esantanche/wandbox/ToolsCutter.odt

Tools: Cutter

I used a cutter to cut plastic profiles for the box.

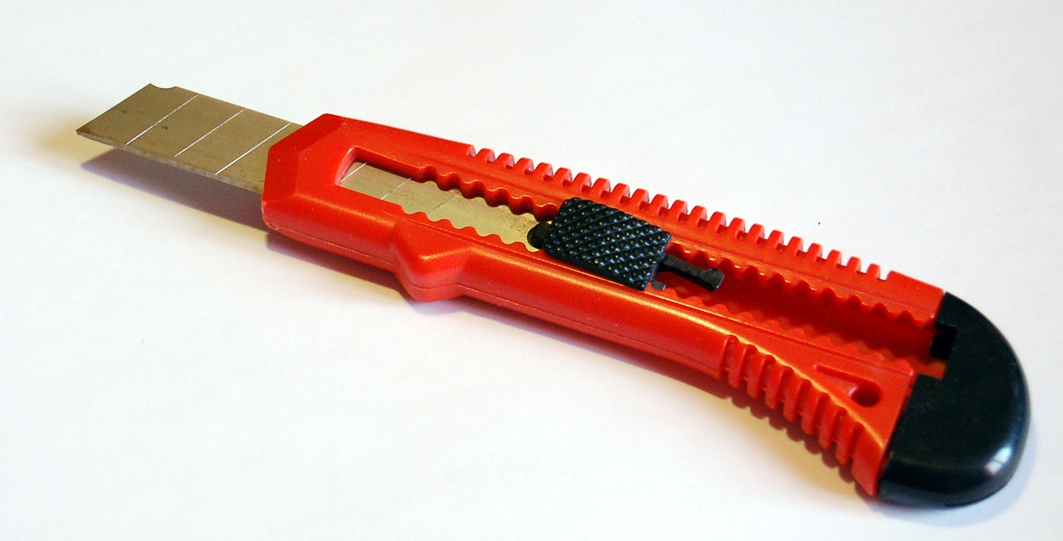
[picture p1: figure]
