esantanche/wandbox/PhotoGallery/011_4mm_box.odt

I changed the drawings to use for the box because I need to use 4mm plywood.

This because I have to use plywood that can be laser cut.

The 6.4mm and 3.2mm plywood I was using in the previous drawings can't be laser cut.

The 3D drawing is basically the same, but now every part is 4mm thick.

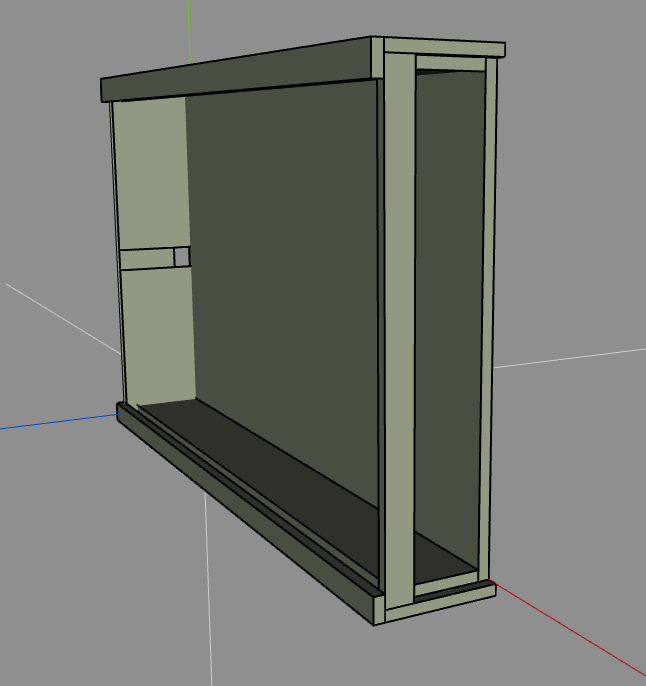
[picture p4: figure]
