esantanche/wandbox/PhotoGallery/010_what_the_box_will_be_like.odt

I started to design the plywood box that will contain Raspberry Pi, monitor and everything.

The 3D design of the box is in the file wandbox-wings3d.wings.

You need the program Wings 3D (http://www.wings3d.com/) to open the file.

I chose Wings 3D because it's simpler to use than other programs.

These are some screen-shots of the box.

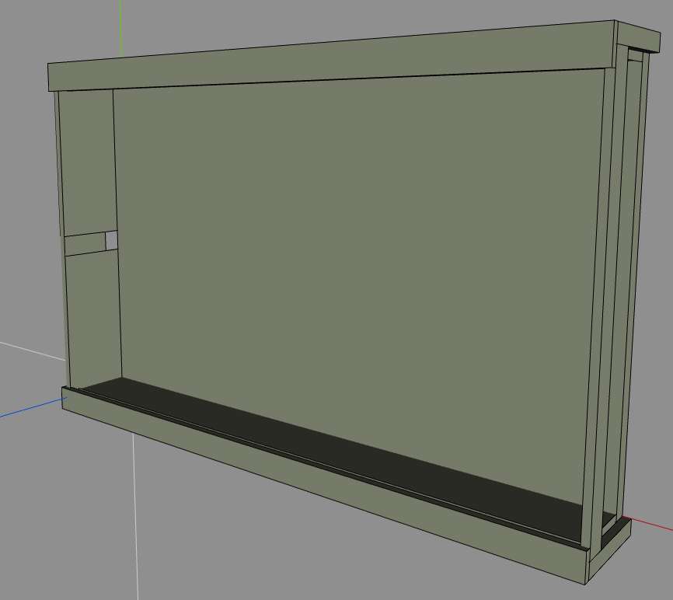
[picture p5: figure]
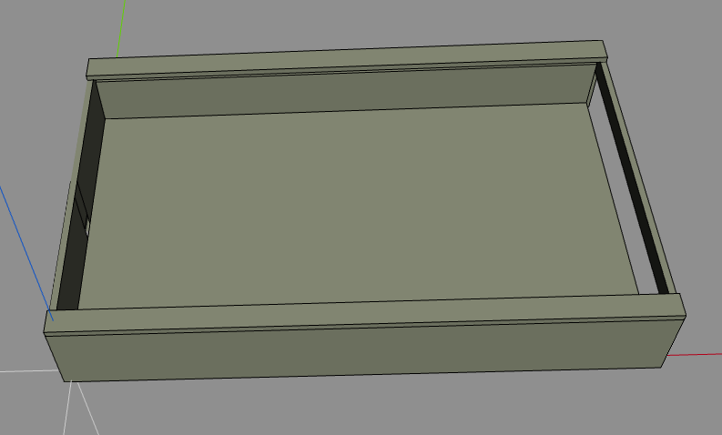
[picture p6: figure]
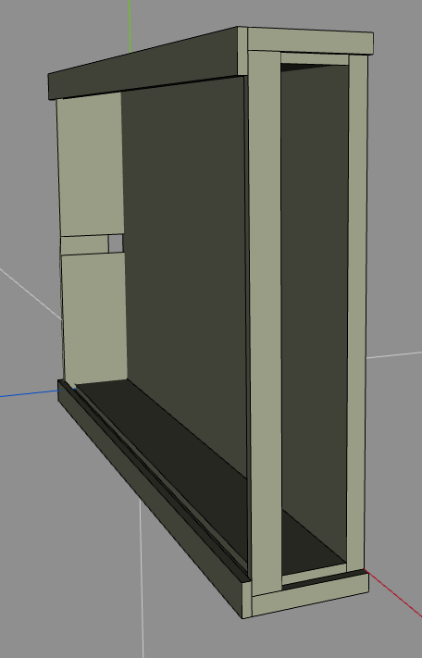
[picture p7: figure]
