esantanche/wandbox/ComponentsFunkyFoamForBatteries.odt

Components:

Funky foam for batteries

Paddybinns (https://www.raspberrypi.org/forums/memberlist.php?mode=viewprofile&u=187239) from https://www.raspberrypi.org/forums recommended I use funky foam to fasten the batteries to the box.

I got this foam from Ryman:

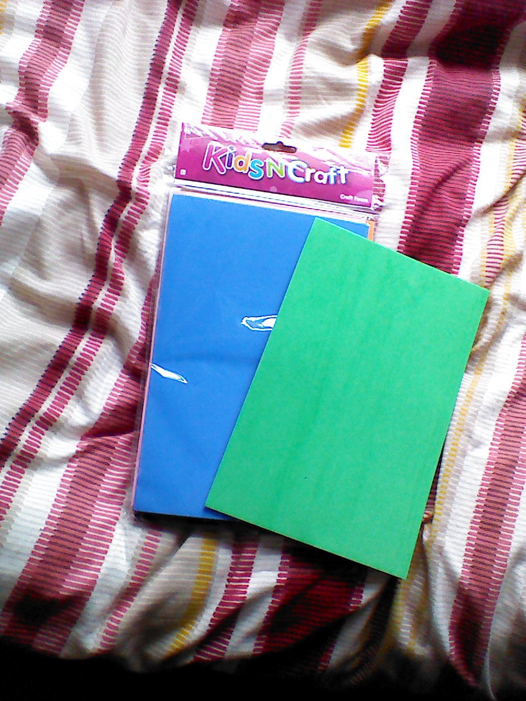
[picture p29: figure]

It's called “Craft Foam”.

It keep the batteries in place very well. I used glue to attach the foam to the wood and to itself.

Other ideas

These are self adhesive: http://www.hobbycraft.co.uk/red-self_adhesive-a4-foam-sheet/571989-1002
