esantanche/wandbox/ComponentsHDMIcable.odt

Components:

HDMI cable

Eventually I got this one:

http://www.cablematic.co.uk/product/HDMI-Cable-HDMI-Type_hyphen_A-Male-to-HDMI_hyphen_A-male-25-cm/

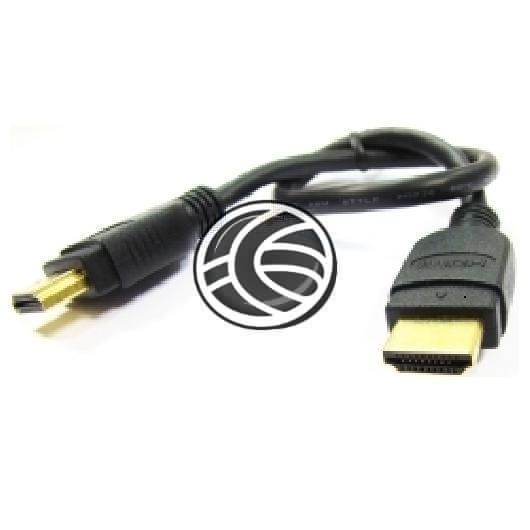
[picture p30: figure]

It's perfect. I had just to move Raspberry Pi and monitor a bit for the cable to fit in.

Before getting this cable I had found a couple of them on Ebay, but they didn't work because the suppliers were sending to me the wrong cable.

They didn't have the 25 cm long one I ordered and sent to me a longer one. But a longer cable was of no use to me because there is little space in the box.
