esantanche/wandbox/ComponentsPowerOnSwitch.odt

Components:

Power on switch

I'm going to use this electronic switch.

You push the micro-button you see on the board and it open or break the circuit.

You apply your power at VIN and you get the output power at VOUT.

From VOUT power goes to Raspberry Pi and monitor. Of course it passes through the voltage regulators first.

You can connect the negative pole to GND on the VIN side and get it on the other side.

The board breaks the GND pole as well, this is better.

This is where the board is from:

http://www.hobbytronics.co.uk/mosfet-power-switch-lv-rev?keyword=switch

I got this board and it came with the pins to be soldered to the board. I'll use connectors to plug into the pins.

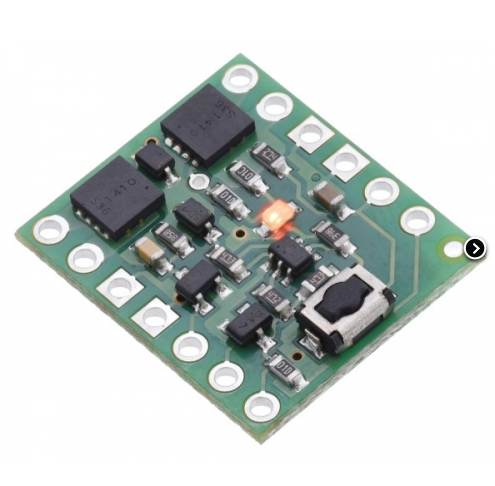
[picture p32: figure]

Connectors

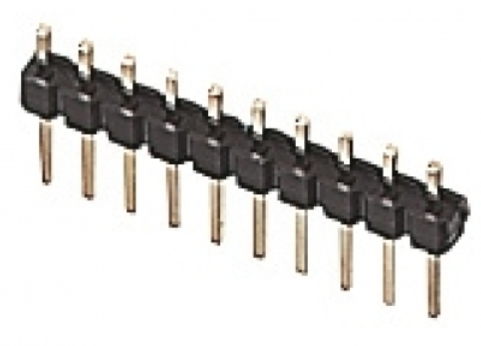
[picture p33: figure]

Pins

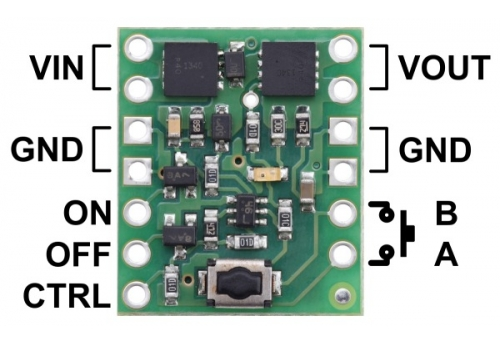
[picture p34: figure]
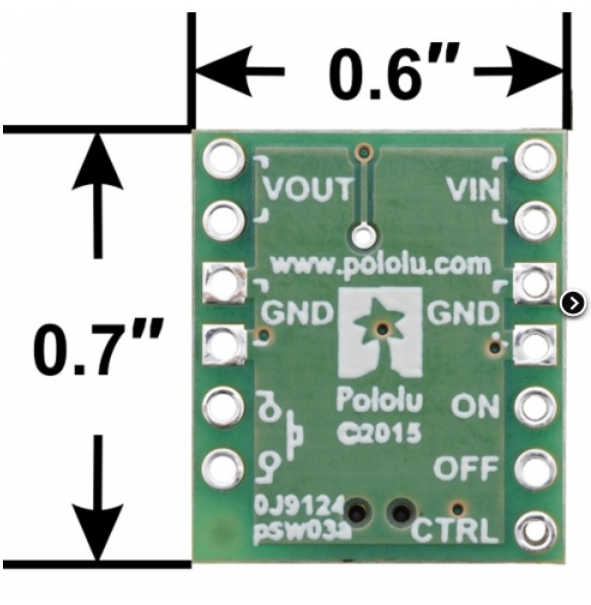
[picture p35: figure]

PIN | Description
A | Connect through momentary switch to pin “B” for standard push-on/push-off operation. Connect through momentary switch to ground for on-only operation.
B | Connect through momentary switch to pin “A” for standard push-on/push-off operation.
ON | A high pulse (> 1 V) on this pin turns on the switch.
OFF | A high pulse (> 1 V) on this pin turns off the switch (e.g. allowing the target device to shut off its own power).
CTRL | This pin directly determines the state of the switch. A high pulse (> 1 V) on this pin turns on the switch; a low pulse (e.g. driving the pin low with a microcontroller output line or pushing a button connected from this pin to ground) turns the switch off. Leave this pin disconnected or floating when not trying to set the switch state. Note that this pin should not be driven high at the same time the “OFF” pin is driven high.
