esantanche/wandbox/ComponentsMonitorAndControlBoard.odt

Components:

Monitor and control board

This is the kit monitor and monitor control board that I bought:

http://www.njytouch.com/products/433-en.html

Some details:

Model: N116B6

This is the control board: http://www.njytouch.com/products/2-en.html.

It has Asian language text for the monitor menu, but I don't care because I'm not going to use the monitor menu.

# Chronology

On 2016-04-02 I got the parcel! I was expecting them not before June!

On 2016-03-19 I asked them if the product is suitable for the UK because I read this on their website:

M.NT68676.2A controller is suitable for Asia-Pacific market. It can support LED/LCD panels which resolution is up to 2048x1152.

On 2016-03-21 they reply saying that the kit is suitable for the UK as well and costs $127 shipping included.

# Information

The monitor should need not more than 20W of power (http://blog.codinghorror.com/how-much-power-does-my-laptop-really-use/). A 2A power supply should be enough. But the maker recommends 4A power supply.

# Package content

1 × HDMI (http://en.wikipedia.org/wiki/HDMI)+DVI (http://en.wikipedia.org/wiki/Digi)+VGA (http://en.wikipedia.org/wiki/Video_Graphics_Array) Controller Board M.NT68676.2A (http://www.njytouch.com/products/2-en.html)

1× 11.6inch 1366* 768 LCD Panel (One of N116B6 (http://www.njytouch.com/products/541-en.html) LP116WH1 B116XW02 LTN116AT01 LTN116AT03 CALL116WA01)

1× LVDS Cable

1× Keyboard with Wire

# Images

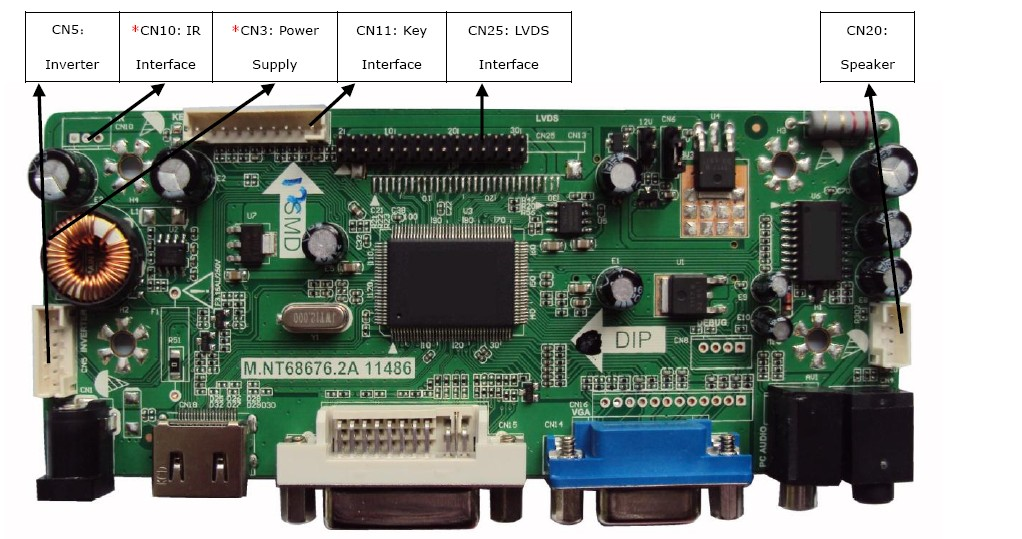
[picture p38: figure]
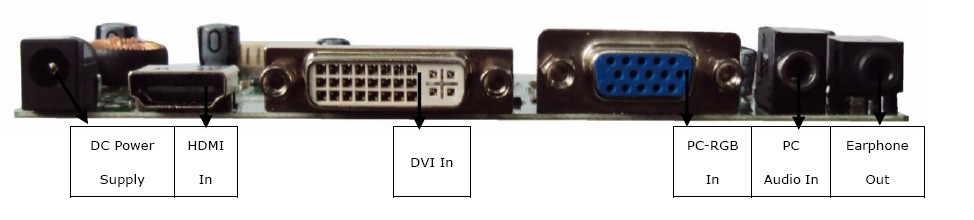
[picture p39: figure]
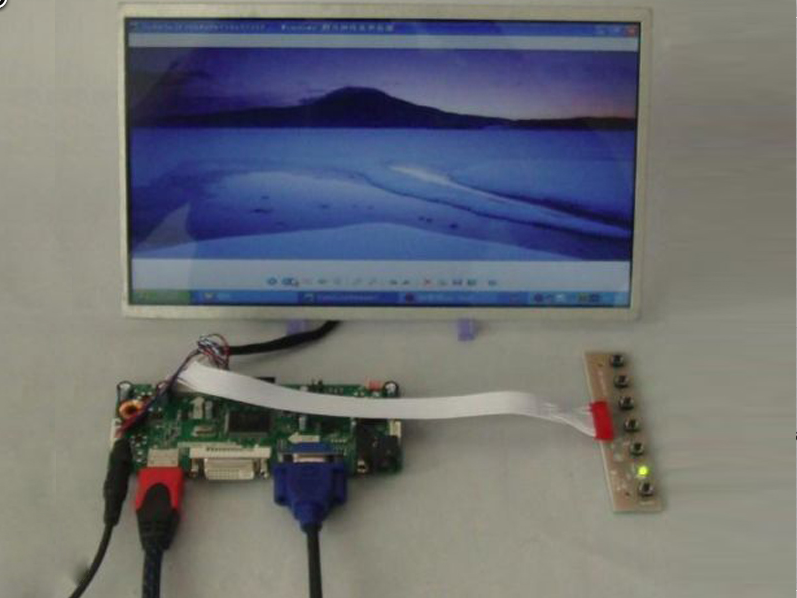
[picture p40: figure]
