esantanche/wandbox/ComponentsSDcard.odt

Components:

SD card

I got this one:

https://www.sandisk.co.uk/home/memory-cards/microsd-cards/extreme-microsd

I got it from Argos, but I can't find it again in their catalogue.

It's a Sandisk Extreme 32 GB MicroSDHC card with

Read Speed: up to 60MB/s

Write Speed: up to 40MB/s

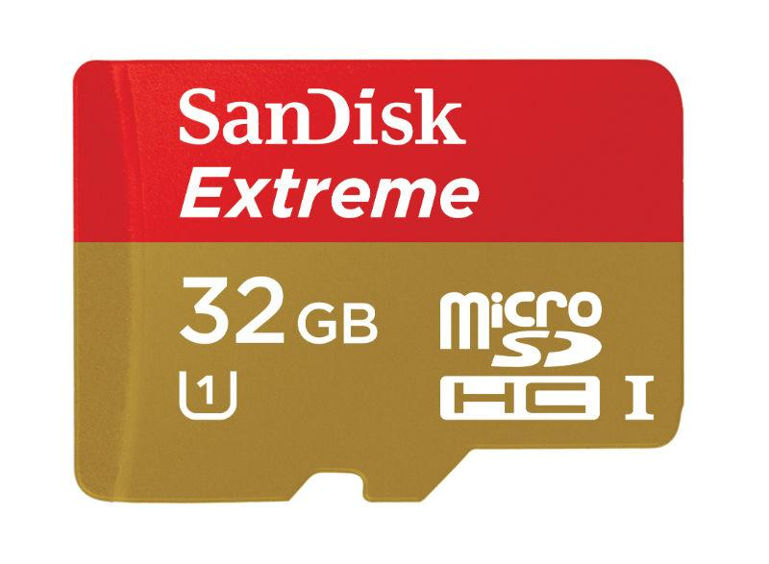
[picture p41: figure]
