esantanche/wandbox/PhotoGallery/012_building_the_box.odt

Just got the parts of the box laser-cut from an 800 mm x 450 mm plywood sheet:

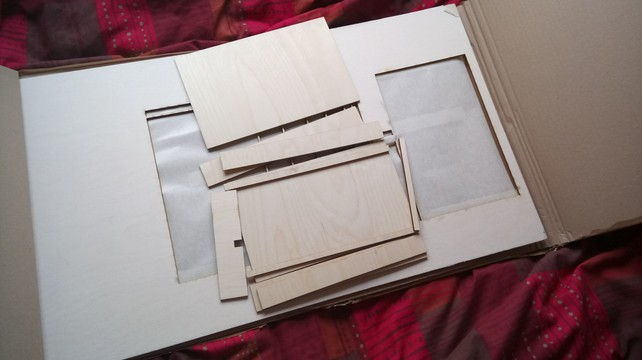
[picture p44: figure]

I started to build the box, but the screws are damaging it.

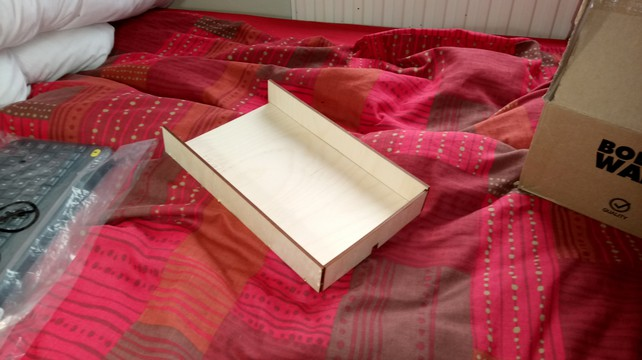
[picture p45: figure]

Glueing some parts.

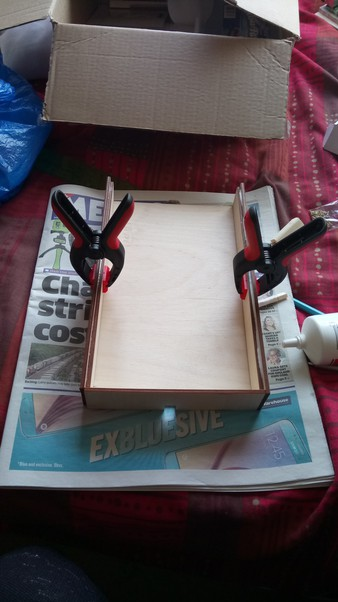
[picture p46: figure]

I found a solution to the problem of screws damaging the wood. I used plastic profiles.

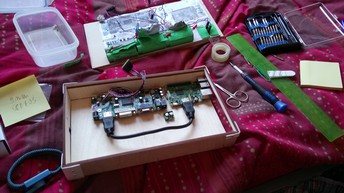
[picture p47: figure]
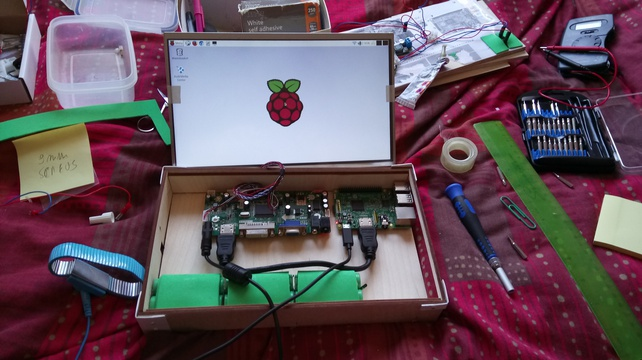
[picture p48: figure]

Building the box and moving components inside it:

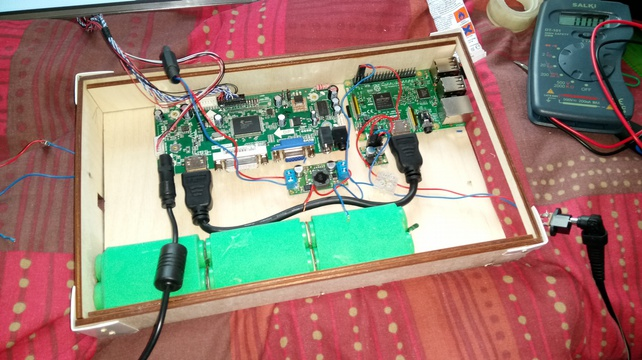
[picture p49: figure]
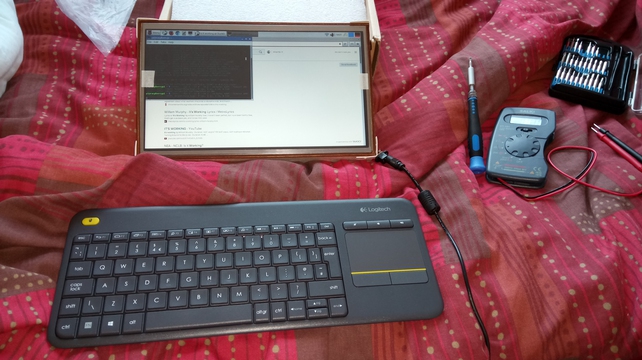
[picture p50: figure]
