esantanche/wandbox/PhotoGallery/013_still_building_the_box.odt

Still building the box. Now testing the power switch.

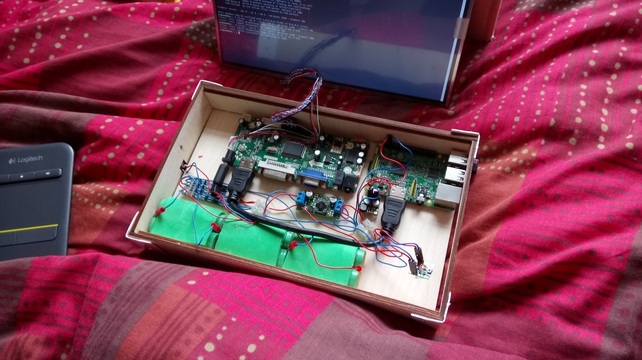
[picture p51: figure]
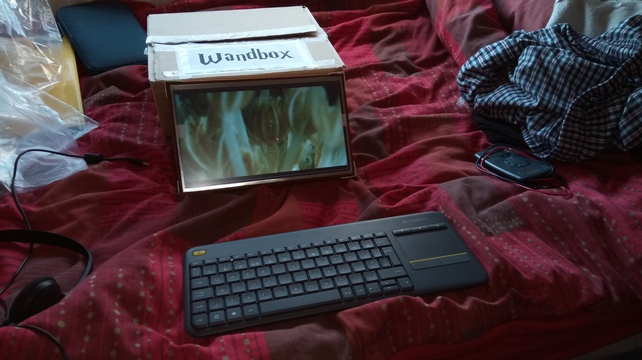
[picture p52: figure]
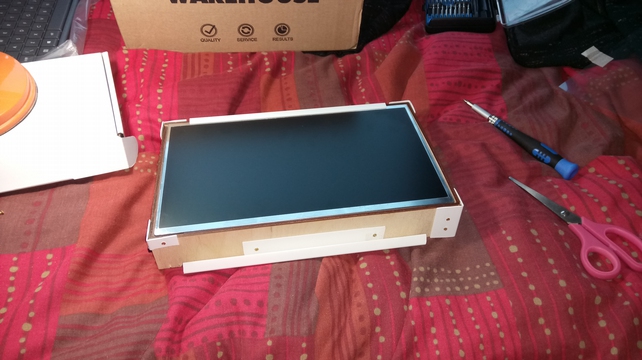
[picture p53: figure]
