esantanche/wandbox/PhotoGallery/003_how_to_fasten_the_monitor?.odt

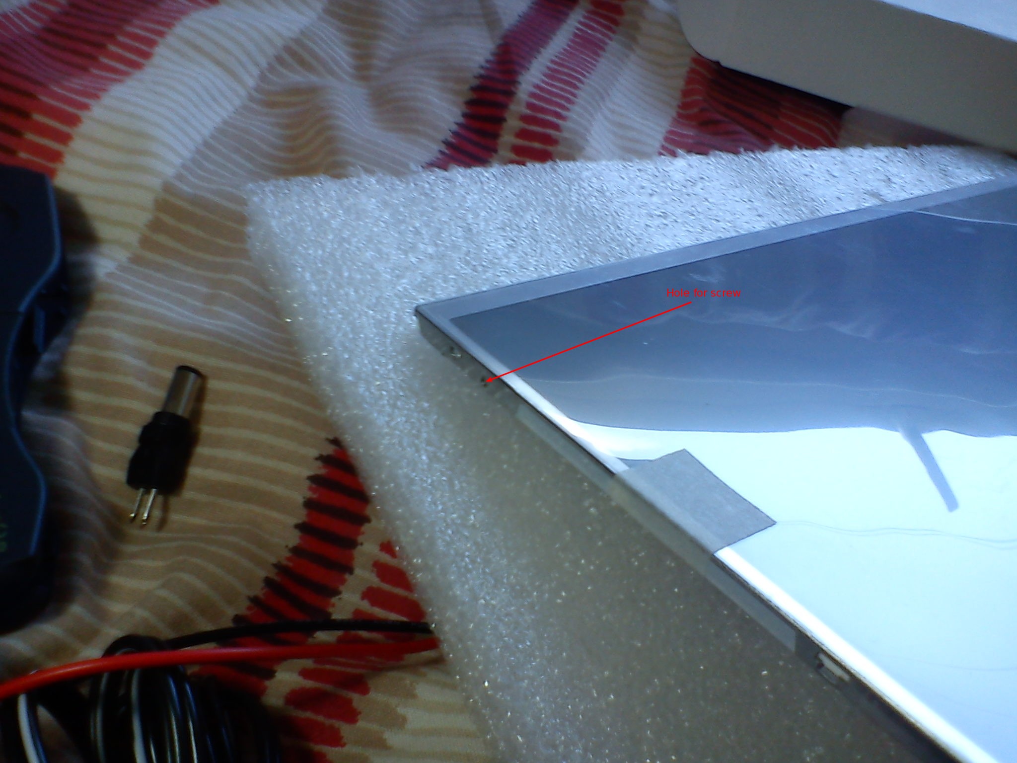
[picture p54: figure]

Now my problem is to find a way to screw the monitor to the plywood box. I don't even have a project for the box yet.

But I'm looking for ideas anyway.

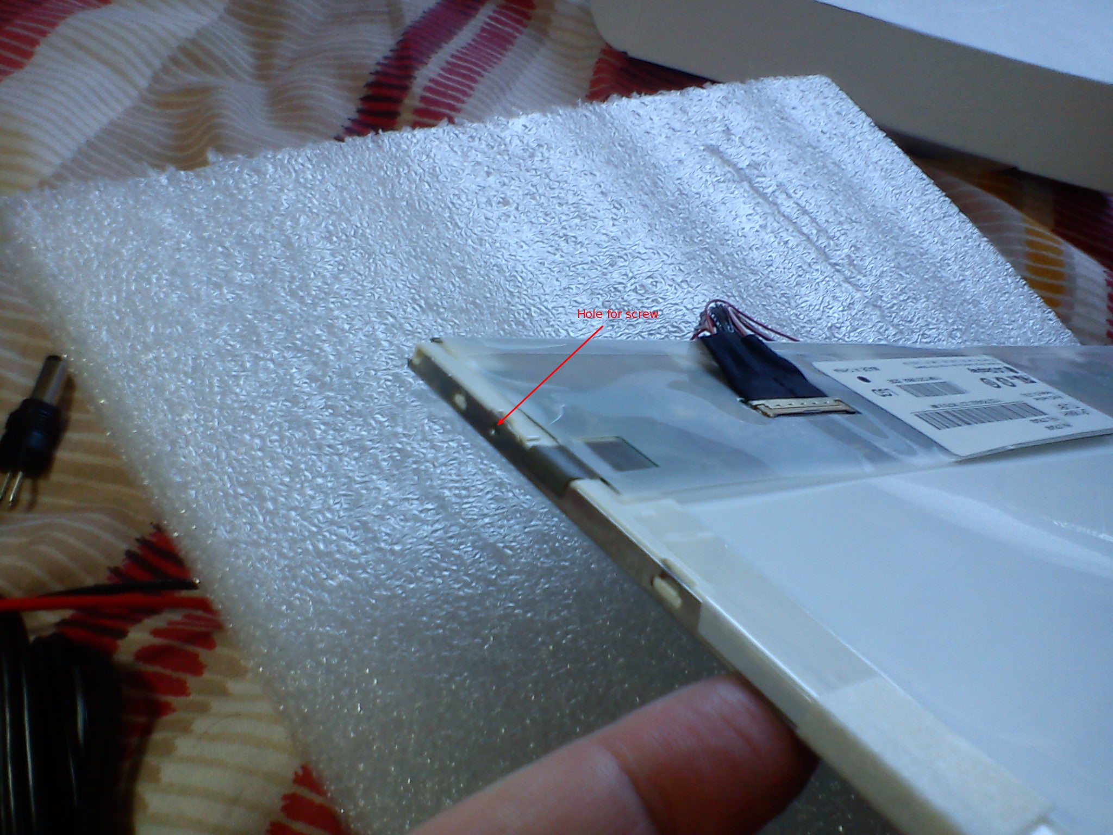
[picture p55: figure]
