esantanche/wandbox/PhotoGallery/007_experiments_with_charging_batteries.odt

Experiments with charging batteries

I'm using a 12V PSU I recovered from an old PC.

With a 12v PSU you can't charge an 11.1V battery because it fully charges at 12.6V.

I used the 13.5V PSU and this time the battery got fully charged.

When I started charging the batteries with the 13.5V PSU, there was a 3.5A current. This is more than the maximum the 13.5V PSU allows.

It worked, but, not to risk damaging the 13.5V PSU it would be better to use a more powerful PSU.

At a given point there was a variable current between 0 and 2.5A.

Eventually the current was zero, which means that the batteries were full. Just there was an occasional 2A current when the batteries lowered their voltage.

I didn't even try with 15V from the PSU because the current would have been even higher.

I guess I need another PSU or I have to use the 13.5V one to fully charge the batteries when the computer is not running and the 12V one only to charge them when the computer is working.

It would be even better not to use the 13.5V PSU to charge the batteries because the current is too high.
