esantanche/wandbox/PhotoGallery/009_more_experiments_with_charging_batteries.odt

Experiments with charging batteries

I did some experiments to see how high are the currents absorbed when batteries are charging and decide how to use my two PSUs.

## Experiment with 12V PSU and not-fully-charged batteries

I'm using the 12V PSU. It can produce a current of maximum 4A.

Raspberry Pi and monitor are on.

The current is 2.4A and becomes 2.5A if I run a stress test on the Raspberry Pi by using the command stress (stress --cpu 8 --io 4 --vm 2 --vm-bytes 128M --timeout 100s).

When I power off Raspberry Pi, the current decreases to 2A.

With Raspberry Pi off, the current gets lower and lower. It goes down to 1.5A, 0.5A, 0.34A, 0.16A.

Eventually it stops. It takes a couple of hours to get here.

I realize that I can't fully charge the batteries if I use a 12V PSU because the batteries are fully charged when they reach 12.6V.

## Experiment with 13.5V PSU and almost charged batteries

Just after having almost charged the batteries by using the 12V PSU, now I use the 13.5V one.

It starts with 2.75A.

In just 15 minutes there is no current, just sometimes the current goes up to 2A then it goes back to zero.

Batteries are charged.

This means that the 12V PSU charged them almost fully and the 13.5V PSU added very little to the charge.

## Experiment to discharge the batteries

I power on Raspberry Pi and monitor and let the batteries discharge.

It takes more than 4 hours for the batteries to go down from 12.6V to 9.5V.

At 9.5V Raspberry Pi and monitor are off.

Batteries are empty.

I think that, when I'll measure batteries' voltage automatically and display it, I'll consider 12V as 100% charge and 10V as 0% charge. So, when batteries' voltage is lower than 10V, I'll pop up an alert. It will be time to shut down Raspberry Pi.

## Experiment with 13.5V PSU and empty batteries

Now batteries are empty.

I use the 13.5V PSU.

Current starts at 3.56A. This is more than the maximum the 13.5V PSU allows.

Current shouldn't be more than 2.4A.

The PSU works, but after 30 minutes I unplug it because it's getting very hot.

I complete charging batteries with the 12V PSU.

It starts with 2A.

## Some conclusions

Even if the 12V PSU doesn't charge batteries fully, it charges them quite a lot.

I'll use the 12V PSU to charge batteries and power Raspberry Pi and monitor.

The 13.5V PSU may be useful to completely charge batteries, but it's not needed.

I can use it with a 12V voltage.

## Other experiments

I should test the 12V PSU with empty batteries and with Raspberry Pi and monitor on.

But it shouldn't exceed 4A.

I may test the 13.5V PSU when set to 12V, but this is less important because I'm not going to use it so much.
