esantanche/wandbox/PhotoGallery/015_Testing_in_the_wild.odt

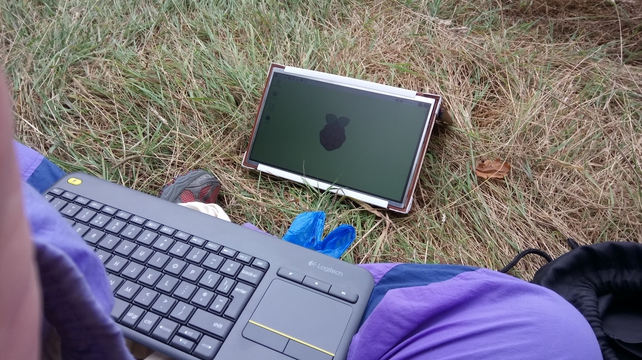
[picture p79: figure]

Testing in the wild!
